skifli/splongle/cart.png

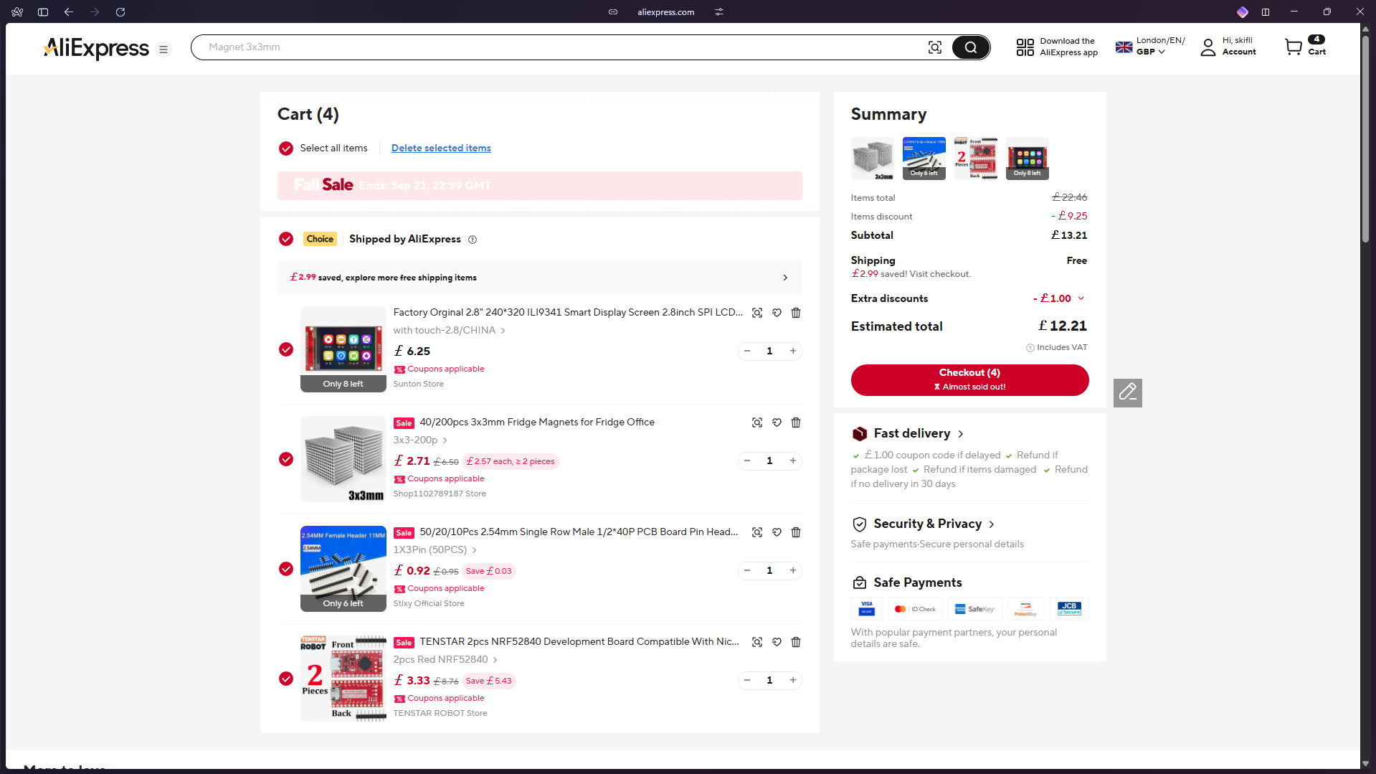
cart.png
